goose35/RetroWiFiModem/images/MyRetroWiFiModemB.jpg

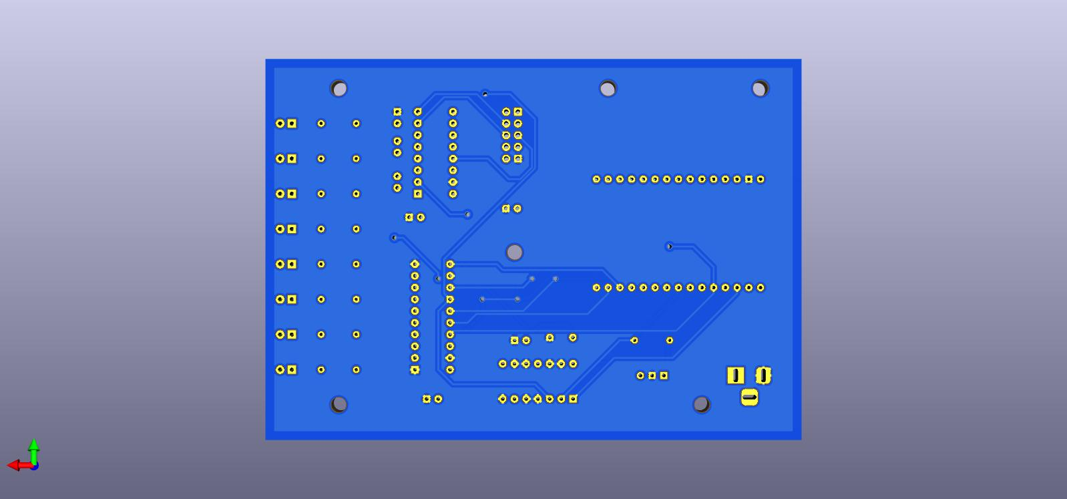
images/MyRetroWiFiModemB.jpg
